Saint-Joe/Vivarium-Controler/quad_24v_controller/CONFIG.h

/************************* Application Info **********************************/

#define APP_NAME        "Quad Controller"
#define CODE_VER        "00.01"

/************************* WiFi Access Point *********************************/

#define WLAN_SSID       "...ssid..."
#define WLAN_PASS       "...password..."

/***************************** MQTT Setup ************************************/

#define MQTT_SERVER      "192.168.1.100"       //MQTT Broker host name (mqtt.domain.com) or ip
#define MQTT_SERVERPORT  1883                   // use 8883 for SSL
#define MQTT_USERNAME    "...mqttuser..."
#define MQTT_PASSWORD    "...mqttpass..."
#define UNIQUE_ID        "...QUAD24TEST..."          //user defined id, useful if you have many sensor packs
